DanielMartensson/STM32-PLC/STM32 PLC for GoobySoft/Core/Src/STM32 PLC/USB.c

/*
 * USB.c
 *
 *  Created on: Jun 13, 2021
 *      Author: Daniel Mårtensson
 */

#include "Functions.h"

/* Private functions */
static uint32_t write_set_can_bus_message_from_gooby_soft(uint32_t byte_index, uint8_t *receive_buf);
static uint32_t write_set_pwm_prescaler_message(uint32_t byte_index, uint8_t *receive_buf);
static uint32_t write_set_adc_gain_message(uint32_t byte_index, uint8_t *receive_buf);
static uint32_t write_set_date_time_message(uint32_t byte_index, uint8_t *receive_buf);
static uint32_t write_set_alarm_a_message(uint32_t byte_index, uint8_t *receive_buf);
static uint32_t write_set_alarm_b_message(uint32_t byte_index, uint8_t *receive_buf);
static uint32_t write_set_PWM_signal_from_gooby_soft(uint32_t byte_index, uint8_t *receive_buf);
static uint32_t write_set_DAC_signal_from_gooby_soft(uint32_t byte_index, uint8_t *receive_buf);
static uint32_t send_back_adc_gains(uint32_t byte_index, uint8_t *receive_buf);
static uint32_t send_back_digital_in_to_gooby_soft(uint32_t byte_index, uint8_t *receive_buf);
static uint32_t send_back_analog_in_to_gooby_soft(uint32_t byte_index, uint8_t *receive_buf);
static uint32_t send_back_analog_differential_in_to_gooby_soft(uint32_t byte_index, uint8_t *receive_buf);
static uint32_t send_back_input_capture_to_gooby_soft(uint32_t byte_index, uint8_t *receive_buf);
static uint32_t send_back_encoder_to_gooby_soft(uint32_t byte_index, uint8_t *receive_buf);
static void send_back_can_bus_message_to_gooby_soft();
static void send_back_pwm_prescalers();
static void send_back_date_time();
static void send_back_alarm_a();
static void send_back_alarm_b();

/*
 * This is a "interrupt" function made by me.
 * CDC_ReceiveCallback(Buf, *Len); should always be implemented inside the function
 * static int8_t CDC_Receive_FS(uint8_t* Buf, uint32_t *Len) at usbd_cdc_if.c
 * where a weak empty function named
 * __weak void CDC_ReceiveCallback(uint8_t* receive_buf, uint32_t receive_len){
 *
 * }
 * is there below
 */

void CDC_ReceiveCallback(uint8_t *receive_buf, uint32_t receive_len) {
	/* Toggle the USB LED */
	STM32_PLC_LED_Set(LED_USB_PROCESS);

	/* Read all bytes as they where packages */
	uint32_t byte_index = 0;
	while (byte_index < receive_len) {
		/* Always add +1 for byte_index because the previous byte index was the message type */
		uint8_t message_type = receive_buf[byte_index++];

		/* Read the message type */
		switch (message_type) {
		case STM32PLC_WRITE_SET_CAN_BUS_MESSAGE_TYPE:
			byte_index = write_set_can_bus_message_from_gooby_soft(byte_index, receive_buf);
			break;
		case STM32PLC_WRITE_SET_PWM_SIGNAL_MESSAGE_TYPE:
			byte_index = write_set_PWM_signal_from_gooby_soft(byte_index, receive_buf);
			break;
		case STM32PLC_WRITE_SET_DAC_SIGNAL_MESSAGE_TYPE:
			byte_index = write_set_DAC_signal_from_gooby_soft(byte_index, receive_buf);
			break;
		case STM32PLC_WRITE_SET_DATE_TIME_MESSAGE_TYPE:
			byte_index = write_set_date_time_message(byte_index, receive_buf);
			break;
		case STM32PLC_WRITE_SET_ALARM_A_MESSAGE_TYPE:
			byte_index = write_set_alarm_a_message(byte_index, receive_buf);
			break;
		case STM32PLC_WRITE_SET_ALARM_B_MESSAGE_TYPE:
			byte_index = write_set_alarm_b_message(byte_index, receive_buf);
			break;
		case STM32PLC_WRITE_SET_PWM_PRESCALER_MESSAGE_TYPE:
			byte_index = write_set_pwm_prescaler_message(byte_index, receive_buf);
			break;
		case STM32PLC_WRITE_SET_ANALOG_INPUT_GAIN_MESSAGE_TYPE:
			byte_index = write_set_adc_gain_message(byte_index, receive_buf);
			break;
		case STM32PLC_SEND_BACK_ANALOG_GAINS_MESSAGE_TYPE:
			byte_index = send_back_adc_gains(byte_index, receive_buf);
			break;
		case STM32PLC_SEND_BACK_PWM_PRESCALERS_MESSAGE_TYPE:
			send_back_pwm_prescalers();
			break;
		case STM32PLC_SEND_BACK_DATE_TIME_MESSAGE_TYPE:
			send_back_date_time();
			break;
		case STM32PLC_SEND_BACK_ALARM_A_MESSAGE_TYPE:
			send_back_alarm_a();
			break;
		case STM32PLC_SEND_BACK_ALARM_B_MESSAGE_TYPE:
			send_back_alarm_b();
			break;
		case STM32PLC_SEND_BACK_DIGITAL_IN_MESSAGE_TYPE:
			byte_index = send_back_digital_in_to_gooby_soft(byte_index, receive_buf);
			break;
		case STM32PLC_SEND_BACK_ANALOG_IN_MESSAGE_TYPE:
			byte_index = send_back_analog_in_to_gooby_soft(byte_index, receive_buf);
			break;
		case STM32PLC_SEND_BACK_ANALOG_DIFFERENTIAL_IN_MESSAGE_TYPE:
			byte_index = send_back_analog_differential_in_to_gooby_soft(byte_index, receive_buf);
			break;
		case STM32PLC_SEND_BACK_INPUT_CAPUTRE_MESSAGE_TYPE:
			byte_index = send_back_input_capture_to_gooby_soft(byte_index, receive_buf);
			break;
		case STM32PLC_SEND_BACK_ENCODER_MESSAGE_TYPE:
			byte_index = send_back_encoder_to_gooby_soft(byte_index, receive_buf);
			break;
		case STM32PLC_SEND_BACK_CAN_MESSAGE_TYPE:
			send_back_can_bus_message_to_gooby_soft();
			break;
		default:
			byte_index = receive_len; /* In case if the switch statement did not understand */
			STM32_PLC_LED_Set(LED_USB_ERROR);
		}
	}
}

static void send_back_can_bus_message_to_gooby_soft() {
	/* Get IDE, ID, DLC and data and if it's new message */
	uint32_t IDE = 0;
	uint32_t ID = 0;
	uint8_t DLC = 0;
	uint8_t data[8] = { 0 };
	bool is_new_message = false;
	STM32_PLC_CAN_Get_ID_Data(&IDE, &ID, &DLC, data, &is_new_message);

	/* Total bytes we can send to GoobySoft */
	uint8_t index = 0;

	/* Message type */
	static uint8_t send_data_array[17] = { 0 };

	/* Read ID */
	send_data_array[index++] = IDE;
	send_data_array[index++] = ID >> 24;
	send_data_array[index++] = ID >> 16;
	send_data_array[index++] = ID >> 8;
	send_data_array[index++] = ID;

	/* DLC data length */
	send_data_array[index++] = DLC;

	/* Fill the data */
	for (uint8_t i = 0; i < 8; i++) {
		send_data_array[index++] = data[i];
	}

	/* If it's new data */
	send_data_array[index++] = is_new_message;

	/* Ending */
	send_data_array[index++] = '\r';
	send_data_array[index++] = '\n';

	/* Send the data via USB */
	CDC_Transmit_FS(send_data_array, index);
}

static uint32_t write_set_can_bus_message_from_gooby_soft(uint32_t byte_index, uint8_t *receive_buf) {
	/* Create the CAN message */
	CAN_TxHeaderTypeDef TxHeader = { 0 };
	TxHeader.IDE = receive_buf[byte_index++]; /* CAN_ID_STD or CAN_ID_EXT */
	uint32_t ID = (receive_buf[byte_index] << 24) | (receive_buf[byte_index + 1] << 16) | (receive_buf[byte_index + 2] << 8) | receive_buf[byte_index + 3];
	byte_index += 4;
	/* Give ID to both StdID and ExtId. The IDE variable determine which one we are going to use */
	TxHeader.StdId = ID;
	TxHeader.ExtId = ID;
	TxHeader.DLC = receive_buf[byte_index++];
	uint8_t data[TxHeader.DLC];
	/* We always sending 8 bytes of data */
	for (uint8_t i = 0; i < 8; i++) {
		if (i < TxHeader.DLC) {
			data[i] = receive_buf[byte_index++];
		} else {
			byte_index++;
		}
	}
	TxHeader.RTR = CAN_RTR_DATA; /* Data frame */
	TxHeader.TransmitGlobalTime = DISABLE;
	STM32_PLC_LED_Set(LED_CAN_USB_PROCESS);
	if (HAL_ERROR == STM32_PLC_CAN_Transmit(data, &TxHeader)) {
		STM32_PLC_LED_Set(LED_CAN_USB_ERROR);
	}

	/* Write OK back */
	uint8_t dataRX[2] = {'\r', '\n'};
	CDC_Transmit_FS(dataRX, 2);

	/* Return byte index value */
	return byte_index;
}

static uint32_t write_set_PWM_signal_from_gooby_soft(uint32_t byte_index, uint8_t *receive_buf) {
	/* What index of PWM */
	uint8_t pwm_index = receive_buf[byte_index++];

	/* Set PWM */
	STM32_PLC_PWM_Set(pwm_index, (receive_buf[byte_index] << 8) | receive_buf[byte_index + 1]);
	byte_index += 2;

	/* Write OK back */
	uint8_t dataRX[2] = {'\r', '\n'};
	CDC_Transmit_FS(dataRX, 2);

	/* Return byte index value */
	return byte_index;
}

static uint32_t write_set_DAC_signal_from_gooby_soft(uint32_t byte_index, uint8_t *receive_buf) {
	/* What index of DAC */
	uint8_t dac_index = receive_buf[byte_index++];

	/* Set PWM */
	STM32_PLC_Analog_Output_Set(dac_index, (receive_buf[byte_index] << 8) | receive_buf[byte_index + 1]);
	byte_index += 2;

	/* Write OK back */
	uint8_t dataRX[2] = {'\r', '\n'};
	CDC_Transmit_FS(dataRX, 2);

	/* Return byte index value */
	return byte_index;
}

static uint32_t send_back_digital_in_to_gooby_soft(uint32_t byte_index, uint8_t *receive_buf) {
	/* Create array of measurements */
	uint8_t send_data_array[3] = { 0 };
	uint8_t index = 0;

	/* What index of digital input */
	uint8_t digital_in_index = receive_buf[byte_index++];

	/* Set digital input */
	send_data_array[index++] = STM32_PLC_Digital_Input_Get(digital_in_index);
	send_data_array[index++] = '\r';
	send_data_array[index++] = '\n';

	/* Send the data via USB */
	CDC_Transmit_FS(send_data_array, index);

	/* Return the byte index */
	return byte_index;
}

static uint32_t send_back_analog_in_to_gooby_soft(uint32_t byte_index, uint8_t *receive_buf) {
	/* Create array of measurements */
	uint8_t send_data_array[4] = { 0 };
	uint8_t index = 0;

	/* What index of analog input */
	uint8_t analog_in_index = receive_buf[byte_index++];

	/* Set analog input value */
	uint16_t adc_value = STM32_PLC_Analog_Input_ADC_Get_Raw(analog_in_index);
	send_data_array[index++] = adc_value >> 8;
	send_data_array[index++] = adc_value;
	send_data_array[index++] = '\r';
	send_data_array[index++] = '\n';

	/* Send the data via USB */
	CDC_Transmit_FS(send_data_array, index);

	/* Return the byte index */
	return byte_index;
}

static uint32_t send_back_analog_differential_in_to_gooby_soft(uint32_t byte_index, uint8_t *receive_buf) {
	/* Create array of measurements */
	uint8_t send_data_array[4] = { 0 };
	uint8_t index = 0;

	/* What index of analog differential input */
	uint8_t analog_differential_in_index = receive_buf[byte_index++];

	/* Set analog differential input value */
	uint16_t dadc_value = STM32_PLC_Analog_Input_DADC_Get_Raw(analog_differential_in_index);
	send_data_array[index++] = dadc_value >> 8;
	send_data_array[index++] = dadc_value;
	send_data_array[index++] = '\r';
	send_data_array[index++] = '\n';

	/* Send the data via USB */
	CDC_Transmit_FS(send_data_array, index);

	/* Return the byte index */
	return byte_index;
}

static uint32_t send_back_input_capture_to_gooby_soft(uint32_t byte_index, uint8_t *receive_buf) {
	/* Create array of measurements */
	uint8_t send_data_array[4] = { 0 };
	uint8_t index = 0;

	/* What index of input capture */
	uint8_t input_capture_index = receive_buf[byte_index++];

	/* Set input capture value */
	uint16_t input_capture_value = STM32_PLC_Input_Capture_Get_Raw(input_capture_index);
	send_data_array[index++] = input_capture_value >> 8;
	send_data_array[index++] = input_capture_value;
	send_data_array[index++] = '\r';
	send_data_array[index++] = '\n';

	/* Send the data via USB */
	CDC_Transmit_FS(send_data_array, index);

	/* Return the byte index */
	return byte_index;
}

static uint32_t send_back_encoder_to_gooby_soft(uint32_t byte_index, uint8_t *receive_buf) {
	/* Create array of measurements */
	uint8_t send_data_array[4] = { 0 };
	uint8_t index = 0;

	/* What index of encoder */
	uint8_t encoder_index = receive_buf[byte_index++];

	/* Set encoder value */
	uint16_t encoder_value = STM32_PLC_Encoder_Get_Raw(encoder_index);
	send_data_array[index++] = encoder_value >> 8;
	send_data_array[index++] = encoder_value;
	send_data_array[index++] = '\r';
	send_data_array[index++] = '\n';

	/* Send the data via USB */
	CDC_Transmit_FS(send_data_array, index);

	/* Return the byte index */
	return byte_index;
}

static uint32_t write_set_pwm_prescaler_message(uint32_t byte_index, uint8_t *receive_buf) {
	/* Read the prescalers */
	uint16_t prescaler_PWM0_PWM3 = receive_buf[byte_index] << 8 | receive_buf[byte_index + 1];
	byte_index += 2;
	uint16_t prescaler_PWM4_PWM7 = receive_buf[byte_index] << 8 | receive_buf[byte_index + 1];
	byte_index += 2;

	/* Set the prescalers */
	STM32_PLC_PWM0_To_PWM3_Set_Prescaler(prescaler_PWM0_PWM3, true);
	STM32_PLC_PWM4_To_PWM7_Set_Prescaler(prescaler_PWM4_PWM7, true);

	/* Write OK back */
	uint8_t dataRX[2] = {'\r', '\n'};
	CDC_Transmit_FS(dataRX, 2);

	/* Return byte index value */
	return byte_index;
}

static uint32_t write_set_adc_gain_message(uint32_t byte_index, uint8_t *receive_buf) {
	/* What type of ADC should be send the gain too ? */
	uint8_t sdadc = receive_buf[byte_index++];

	/* Get the configuration index */
	uint8_t configuration_index = receive_buf[byte_index++];

	/* Read the gain and apply it */
	uint8_t gain = receive_buf[byte_index++];

	/* Set the gain */
	STM32_PLC_Analog_Input_Set_Gain(sdadc, configuration_index, gain, true);

	/* Write OK back */
	uint8_t dataRX[2] = {'\r', '\n'};
	CDC_Transmit_FS(dataRX, 2);

	/* Return byte index value */
	return byte_index;
}

static uint32_t write_set_date_time_message(uint32_t byte_index, uint8_t *receive_buf) {
	uint8_t year = receive_buf[byte_index++];
	uint8_t month = receive_buf[byte_index++];
	uint8_t date = receive_buf[byte_index++];
	uint8_t week_day = receive_buf[byte_index++];
	uint8_t hours = receive_buf[byte_index++];
	uint8_t minutes = receive_buf[byte_index++];
	STM32_PLC_RTC_Set_Date(date, week_day, month, year);
	STM32_PLC_RTC_Set_Time(0, minutes, hours);

	/* Write OK back */
	uint8_t dataRX[2] = {'\r', '\n'};
	CDC_Transmit_FS(dataRX, 2);

	return byte_index;
}

static uint32_t write_set_alarm_a_message(uint32_t byte_index, uint8_t *receive_buf) {
	uint8_t date = receive_buf[byte_index++];
	uint8_t hours = receive_buf[byte_index++];
	uint8_t minutes = receive_buf[byte_index++];
	uint8_t enable = receive_buf[byte_index++];
	STM32_PLC_RTC_Set_Alarm_A(minutes, hours, date);
	STM32_PLC_RTC_Enable_Alarm_A(enable);

	/* Write OK back */
	uint8_t dataRX[2] = {'\r', '\n'};
	CDC_Transmit_FS(dataRX, 2);

	return byte_index;
}

static uint32_t write_set_alarm_b_message(uint32_t byte_index, uint8_t *receive_buf) {
	uint8_t week_day = receive_buf[byte_index++];
	uint8_t hours = receive_buf[byte_index++];
	uint8_t minutes = receive_buf[byte_index++];
	uint8_t enable = receive_buf[byte_index++];
	STM32_PLC_RTC_Set_Alarm_B(minutes, hours, week_day);
	STM32_PLC_RTC_Enable_Alarm_B(enable);

	/* Write OK back */
	uint8_t dataRX[2] = {'\r', '\n'};
	CDC_Transmit_FS(dataRX, 2);

	return byte_index;
}

static uint32_t send_back_adc_gains(uint32_t byte_index, uint8_t *receive_buf) {
	/* Create array of gains */
	uint8_t send_data_array[5] = { 0 };
	uint8_t index = 0;

	/* Get sdadc index */
	uint8_t sdadc_index = receive_buf[byte_index++];

	/* Get the gains */
	uint8_t gain_for_configuration_index_0, gain_for_configuration_index_1, gain_for_configuration_index_2;
	switch (sdadc_index) {
	case 0:
		STM32_PLC_Flash_Get_ADC_Gains_For_SDADC_1(&gain_for_configuration_index_0, &gain_for_configuration_index_1, &gain_for_configuration_index_2);
		break;
	case 1:
		STM32_PLC_Flash_Get_ADC_Gains_For_SDADC_2(&gain_for_configuration_index_0, &gain_for_configuration_index_1, &gain_for_configuration_index_2);
		break;
	case 2:
		STM32_PLC_Flash_Get_ADC_Gains_For_SDADC_3(&gain_for_configuration_index_0, &gain_for_configuration_index_1, &gain_for_configuration_index_2);
		break;
	}

	/* Fill the array */
	send_data_array[index++] = gain_for_configuration_index_0;
	send_data_array[index++] = gain_for_configuration_index_1;
	send_data_array[index++] = gain_for_configuration_index_2;
	send_data_array[index++] = '\r';
	send_data_array[index++] = '\n';

	/* Send the data via USB */
	CDC_Transmit_FS(send_data_array, index);

	/* Return index */
	return byte_index;
}

static void send_back_pwm_prescalers() {
	/* Create array of prescalers */
	uint8_t send_data_array[6] = { 0 };
	uint8_t index = 0;

	/* Get the prescalers */
	uint16_t prescaler_for_PWM_0_3, prescaler_for_PWM_4_7;
	STM32_PLC_Flash_Get_PWM_Prescalers(&prescaler_for_PWM_0_3, &prescaler_for_PWM_4_7);

	/* Fill the array */
	send_data_array[index++] = prescaler_for_PWM_0_3 >> 8;
	send_data_array[index++] = prescaler_for_PWM_0_3;
	send_data_array[index++] = prescaler_for_PWM_4_7 >> 8;
	send_data_array[index++] = prescaler_for_PWM_4_7;
	send_data_array[index++] = '\r';
	send_data_array[index++] = '\n';

	/* Send the data via USB */
	CDC_Transmit_FS(send_data_array, index);
}

static void send_back_date_time() {
	/* Get date time */
	uint8_t year, month, date, week_day, hours, minutes, seconds;
	STM32_PLC_RTC_Get_Date(&week_day, &date, &month, &year);
	STM32_PLC_RTC_Get_Time(&seconds, &minutes, &hours);

	/* Create array */
	uint8_t send_data_array[8] = { 0 };
	uint8_t index = 0;

	/* Fill the array */
	send_data_array[index++] = year;
	send_data_array[index++] = month;
	send_data_array[index++] = date;
	send_data_array[index++] = week_day;
	send_data_array[index++] = hours;
	send_data_array[index++] = minutes;
	send_data_array[index++] = '\r';
	send_data_array[index++] = '\n';

	/* Send the data via USB */
	CDC_Transmit_FS(send_data_array, index);
}

static void send_back_alarm_a() {
	/* Get alarm A */
	uint8_t date, hours, minutes, enabled, activated;
	STM32_PLC_RTC_Get_Alarm_A(&date, &hours, &minutes);
	enabled = STM32_PLC_RTC_Alarm_A_Is_Enabled();
	activated = STM32_PLC_RTC_Alarm_A_Is_Activated();

	/* Create array */
	uint8_t send_data_array[7] = { 0 };
	uint8_t index = 0;

	/* Fill the array */
	send_data_array[index++] = date;
	send_data_array[index++] = hours;
	send_data_array[index++] = minutes;
	send_data_array[index++] = enabled;
	send_data_array[index++] = activated;
	send_data_array[index++] = '\r';
	send_data_array[index++] = '\n';

	/* Send the data via USB */
	CDC_Transmit_FS(send_data_array, index);
}

static void send_back_alarm_b() {
	/* Get alarm B */
	uint8_t week_day, hours, minutes, enabled, activated;
	STM32_PLC_RTC_Get_Alarm_B(&week_day, &hours, &minutes);
	enabled = STM32_PLC_RTC_Alarm_B_Is_Enabled();
	activated = STM32_PLC_RTC_Alarm_B_Is_Activated();

	/* Create array */
	uint8_t send_data_array[7] = { 0 };
	uint8_t index = 0;

	/* Fill the array */
	send_data_array[index++] = week_day;
	send_data_array[index++] = hours;
	send_data_array[index++] = minutes;
	send_data_array[index++] = enabled;
	send_data_array[index++] = activated;
	send_data_array[index++] = '\r';
	send_data_array[index++] = '\n';


	/* Send the data via USB */
	CDC_Transmit_FS(send_data_array, index);
}
