DanielMartensson/STM32-PLC/STM32 PLC for GoobySoft/Core/Src/STM32 PLC/Functions.h

/*
 * Functions.h
 *
 *  Created on: Jun 13, 2021
 *      Author: Daniel Mårtensson
 */

#ifndef SRC_STM32_PLC_FUNCTIONS_H_
#define SRC_STM32_PLC_FUNCTIONS_H_

/* C standard library */
#include <stdbool.h>
#include <stdint.h>
#include <string.h>

/* Project includes */
#include "main.h"
#include "usbd_cdc_if.h"
#include "Open SAE J1939/Open_SAE_J1939/Open_SAE_J1939.h"


// Message types for STM32 PLC
typedef enum {
	STM32PLC_SEND_BACK_CAN_MESSAGE_TYPE,
	STM32PLC_SEND_BACK_DIGITAL_IN_MESSAGE_TYPE,
	STM32PLC_SEND_BACK_ANALOG_IN_MESSAGE_TYPE,
	STM32PLC_SEND_BACK_ANALOG_DIFFERENTIAL_IN_MESSAGE_TYPE,
	STM32PLC_SEND_BACK_INPUT_CAPUTRE_MESSAGE_TYPE,
	STM32PLC_SEND_BACK_ENCODER_MESSAGE_TYPE,
	STM32PLC_SEND_BACK_PWM_PRESCALERS_MESSAGE_TYPE,
	STM32PLC_SEND_BACK_ANALOG_GAINS_MESSAGE_TYPE,
	STM32PLC_SEND_BACK_DATE_TIME_MESSAGE_TYPE,
	STM32PLC_SEND_BACK_ALARM_A_MESSAGE_TYPE,
	STM32PLC_SEND_BACK_ALARM_B_MESSAGE_TYPE,
	STM32PLC_WRITE_SET_CAN_BUS_MESSAGE_TYPE,
	STM32PLC_WRITE_SET_PWM_SIGNAL_MESSAGE_TYPE,
	STM32PLC_WRITE_SET_DAC_SIGNAL_MESSAGE_TYPE,
	STM32PLC_WRITE_SET_ANALOG_INPUT_GAIN_MESSAGE_TYPE,
	STM32PLC_WRITE_SET_PWM_PRESCALER_MESSAGE_TYPE,
	STM32PLC_WRITE_SET_DATE_TIME_MESSAGE_TYPE,
	STM32PLC_WRITE_SET_ALARM_A_MESSAGE_TYPE,
	STM32PLC_WRITE_SET_ALARM_B_MESSAGE_TYPE,
	STM32PLC_ACKNOWLEDGEMENT_MESSAGE_TYPE
}STM32PLC;

#define LED_USB_ERROR 0b101
#define LED_CAN_ERROR 0b011
#define LED_CAN_USB_ERROR 0b111
#define LED_USB_PROCESS 0b100
#define LED_CAN_PROCESS 0b010
#define LED_CAN_USB_PROCESS 0b110

/* Turn on the LED's */
void STM32_PLC_LED();
void STM32_PLC_LED_Set(uint8_t binary_value);

/* PWM functions */
void STM32_PLC_PWM(TIM_HandleTypeDef *htim2, TIM_HandleTypeDef *htim5);
void STM32_PLC_PWM_Set(uint8_t i, uint16_t ON_Period);
uint16_t STM32_PLC_PWM_Get(uint8_t i);
void STM32_PLC_PWM_Reset();
void STM32_PLC_PWM0_To_PWM3_Set_Prescaler(uint16_t prescaler, bool save_to_flash);
void STM32_PLC_PWM4_To_PWM7_Set_Prescaler(uint16_t prescaler, bool save_to_flash);
uint32_t STM32_PLC_PWM0_To_PWM3_Get_Prescaler();
uint32_t STM32_PLC_PWM4_To_PWM7_Get_Prescaler();

/* Input capture */
void STM32_PLC_Input_Capture(TIM_HandleTypeDef* htim17, TIM_HandleTypeDef* htim16, TIM_HandleTypeDef* htim15);
uint16_t STM32_PLC_Input_Capture_Get_Raw(uint8_t i);
float STM32_PLC_Input_Capture_Get_Calibrated(uint8_t i);

/* Counters */
void STM32_PLC_Encoder(TIM_HandleTypeDef* htim4, TIM_HandleTypeDef* htim19, TIM_HandleTypeDef* htim3);
int16_t STM32_PLC_Encoder_Get_Raw(uint8_t i);
float STM32_PLC_Encoder_Get_Calibrated(uint8_t i);
void STM32_PLC_Encoder_Set_Calibration(uint8_t pulses_index, uint16_t pulses, bool save_to_flash);
void STM32_PLC_Encoder_Get_Calibration(uint8_t pulses_index, uint16_t *pulses);

/* Pulse counters */
void STM32_PLC_Pulse_Count_Set(uint8_t i);
uint32_t STM32_PLC_Pulse_Count_Get(uint8_t i);
void STM32_PLC_Pulse_Count_Reset();

/* Analog Output */
void STM32_PLC_Analog_Output(DAC_HandleTypeDef *hdac1, DAC_HandleTypeDef *hdac2, TIM_HandleTypeDef *htim6);
void STM32_PLC_Analog_Output_Set(uint8_t i, uint16_t output);
void STM32_PLC_Analog_Output_Reset();
uint16_t STM32_PLC_Analog_Output_Get(uint8_t i);

/* Digital Input */
uint16_t STM32_PLC_Digital_Input_Get(uint8_t i);

/* Analog input */
void STM32_PLC_Analog_Input(TIM_HandleTypeDef* htim12, TIM_HandleTypeDef* htim13, SDADC_HandleTypeDef* hsdadc1, SDADC_HandleTypeDef* hsdadc2, SDADC_HandleTypeDef* hsdadc3);
void STM32_PLC_Analog_Input_Set_Gain(uint8_t sdadc, uint8_t configuration_index, uint8_t gain, bool save_to_flash);
void STM32_PLC_Analog_Input_Get_Gain(uint8_t sdadc, uint8_t configuration_index[]);
uint16_t STM32_PLC_Analog_Input_ADC_Get_Raw(uint8_t i);
float STM32_PLC_Analog_Input_ADC_Get_Calibrated(uint8_t i);
int16_t STM32_PLC_Analog_Input_DADC_Get_Raw(uint8_t i);
float STM32_PLC_Analog_Input_DADC_Get_Calibrated(uint8_t i);
void STM32_PLC_Analog_Input_Set_Calibration(uint8_t input_index, float scalar, float bias, bool save_to_flash);

/* CAN */
void STM32_PLC_CAN(CAN_HandleTypeDef *hcan);
HAL_StatusTypeDef STM32_PLC_CAN_Transmit(uint8_t TxData[], CAN_TxHeaderTypeDef *TxHeader);
void STM32_PLC_CAN_Get_ID_Data(uint32_t *_IDE, uint32_t *_ID, uint8_t *_DLC, uint8_t data[], bool *_is_new_message);

/* Flash */
void STM32_PLC_Flash_Set_PWM_Prescaler_For_PWM_0_3(uint16_t prescaler);
void STM32_PLC_Flash_Set_PWM_Prescaler_For_PWM_4_7(uint16_t prescaler);
void STM32_PLC_Flash_Set_Alarm_Enable(bool alarm_A_enabled, bool alarm_B_enabled);
void STM32_PLC_Flash_Set_LCD_Calibration(float Scale_X, float Scale_Y, float Bias_X, float Bias_Y);
void STM32_PLC_Flash_Set_J1939_This_ECU_Address(uint8_t this_ECU_address);
void STM32_PLC_Flash_Set_Analog_Input_Calibration(uint8_t input_index, float scalar, float bias);
void STM32_PLC_Flash_Set_Encoder_Pulses(uint8_t pulses_index, uint16_t pulses);
void STM32_PLC_Flash_Set_ADC_Gain_For_Configuration_Index_0(uint8_t sdadc, uint8_t gain);
void STM32_PLC_Flash_Set_ADC_Gain_For_Configuration_Index_1(uint8_t sdadc, uint8_t gain);
void STM32_PLC_Flash_Set_ADC_Gain_For_Configuration_Index_2(uint8_t sdadc, uint8_t gain);
void STM32_PLC_Flash_Get_PWM_Prescalers(uint16_t *prescaler, uint16_t *prescaler_for_PWM_4_7);
void STM32_PLC_Flash_Get_Alarm_Enables(bool *alarm_A_enabled, bool *alarm_B_enabled);
void STM32_PLC_Flash_Get_LCD_Calibration(float *Scale_X, float *Scale_Y, float *Bias_X, float *Bias_Y);
void STM32_PLC_Flash_Get_J1939_This_ECU_Address(uint8_t *this_ECU_address);
void STM32_PLC_Flash_Get_Analog_Input_Calibration(uint8_t input_index, float *scalar, float *bias);
void STM32_PLC_Flash_Get_Encoder_Pulses(uint8_t pulses_index, uint16_t *pulses);
void STM32_PLC_Flash_Get_ADC_Gains_For_SDADC_1(uint8_t *gain_for_configuration_index_0, uint8_t *gain_for_configuration_index_1, uint8_t *gain_for_configuration_index_2);
void STM32_PLC_Flash_Get_ADC_Gains_For_SDADC_2(uint8_t *gain_for_configuration_index_0, uint8_t *gain_for_configuration_index_1, uint8_t *gain_for_configuration_index_2);
void STM32_PLC_Flash_Get_ADC_Gains_For_SDADC_3(uint8_t *gain_for_configuration_index_0, uint8_t *gain_for_configuration_index_1, uint8_t *gain_for_configuration_index_2);

/* RTC */
void STM32_PLC_RTC(RTC_HandleTypeDef *hrtc);
void STM32_PLC_RTC_Get_Date(uint8_t *week_day, uint8_t *date, uint8_t *month, uint8_t *year);
void STM32_PLC_RTC_Set_Date(uint8_t date, uint8_t week_day, uint8_t month, uint8_t year);
void STM32_PLC_RTC_Get_Time(uint8_t *seconds, uint8_t *minutes, uint8_t *hours);
void STM32_PLC_RTC_Set_Time(uint8_t seconds, uint8_t minutes, uint8_t hours);
void STM32_PLC_RTC_Get_Alarm_A(uint8_t *date, uint8_t *hours, uint8_t *minutes);
void STM32_PLC_RTC_Get_Alarm_B(uint8_t *week_day, uint8_t *hours, uint8_t *minutes);
void STM32_PLC_RTC_Set_Alarm_A(uint8_t minutes, uint8_t hours, uint8_t date);
void STM32_PLC_RTC_Set_Alarm_B(uint8_t minutes, uint8_t hours, uint8_t week_day);
void STM32_PLC_RTC_Deactivate_Alarm_A();
void STM32_PLC_RTC_Enable_Alarm_A(bool enable);
bool STM32_PLC_RTC_Alarm_A_Is_Enabled();
bool STM32_PLC_RTC_Alarm_A_Is_Activated();
void STM32_PLC_RTC_Deactivate_Alarm_B();
void STM32_PLC_RTC_Enable_Alarm_B(bool enable);
bool STM32_PLC_RTC_Alarm_B_Is_Enabled();
bool STM32_PLC_RTC_Alarm_B_Is_Activated();

/* LCD */
void STM32_PLC_LCD(SPI_HandleTypeDef *lcdSpi, SPI_HandleTypeDef *touchSpi, GPIO_TypeDef *LCD_CS_PORT, uint16_t LCD_CS_PIN, GPIO_TypeDef *LCD_DC_PORT, uint16_t LCD_DC_PIN, GPIO_TypeDef *TOUCH_CS_PORT, uint16_t TOUCH_CS_PIN);
void STM32_PLC_LCD_Calibrate_Touch();
bool STM32_PLC_LCD_Is_Pressed();
void STM32_PLC_LCD_Get_Touch_Calibration_Parameters(float *Scale_X, float *Scale_Y, float *Bias_X, float *Bias_Y);
void STM32_PLC_LCD_Set_Touch_Calibration_Parameters(float Scale_X, float Scale_Y, float Bias_X, float Bias_Y);
void STM32_PLC_LCD_Get_Touch_Data();


#endif /* SRC_STM32_PLC_FUNCTIONS_H_ */
